RasmusKoit/pipar/.extra/pipar_pcb.png

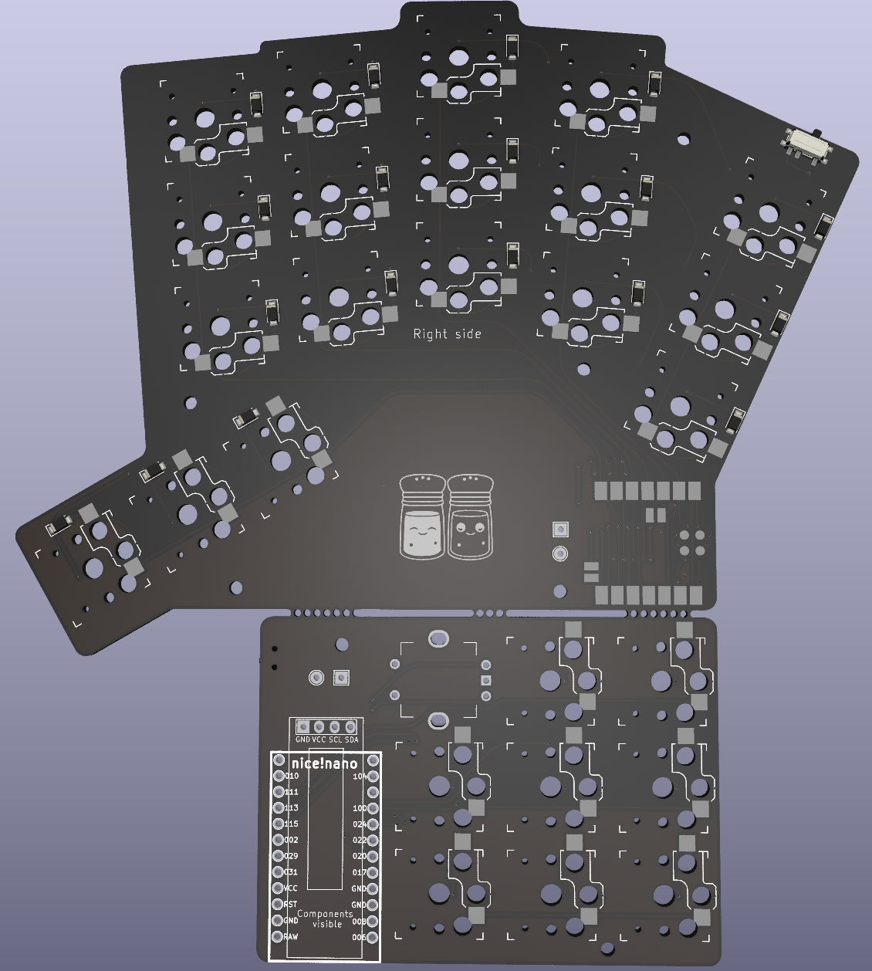
.extra/pipar_pcb.png
